ersatzavian/yellow_fuzz/sims/barbershop/1k_fft.PNG

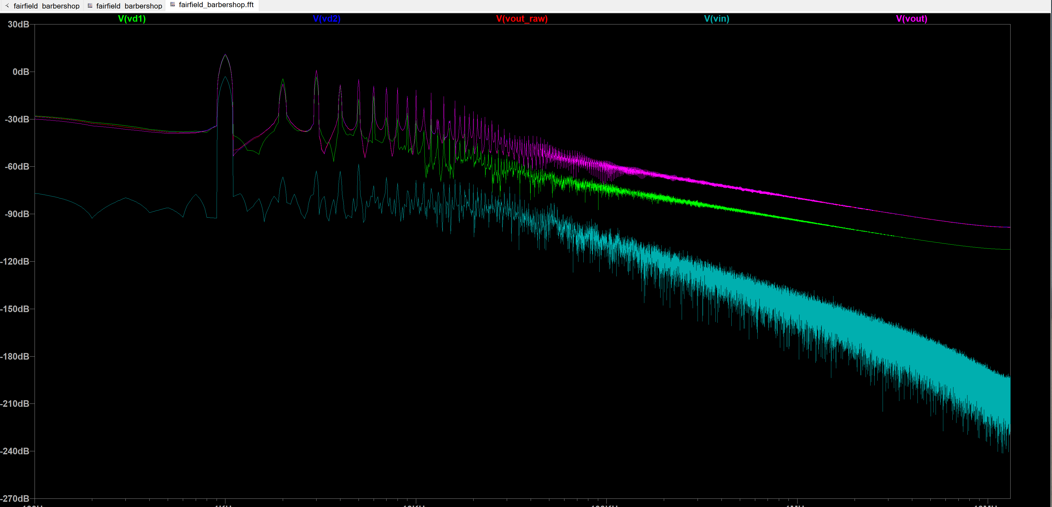
sims/barbershop/1k_fft.PNG
