ersatzavian/yellow_fuzz/sims/barbershop/1k_transient.PNG

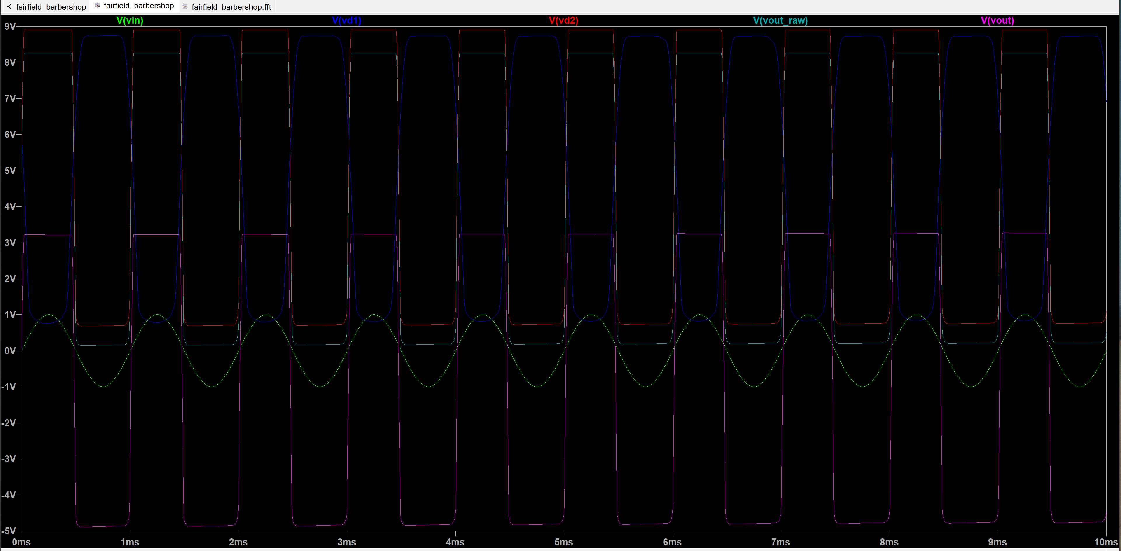
sims/barbershop/1k_transient.PNG
