ersatzavian/yellow_fuzz/sims/barbershop/base.PNG

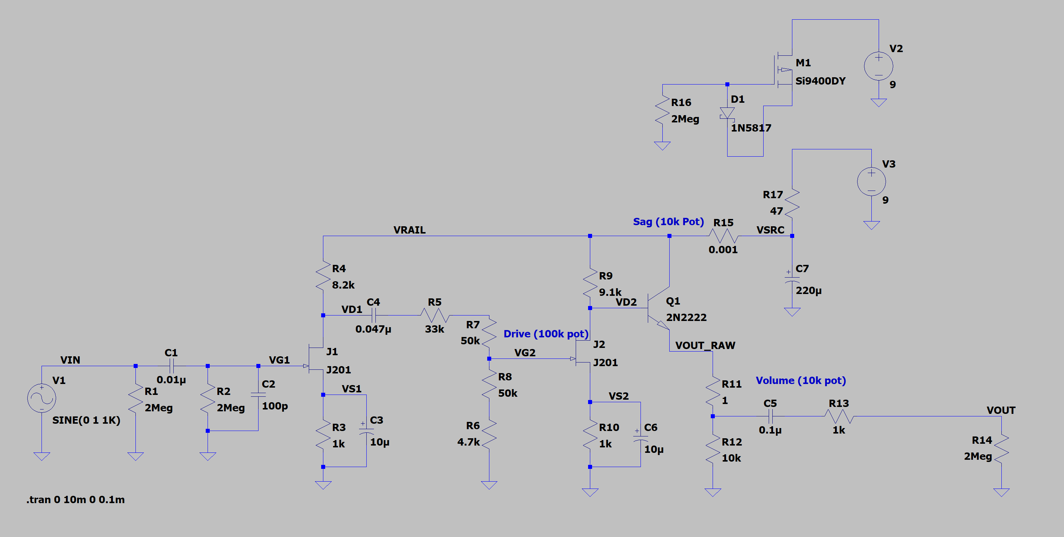
sims/barbershop/base.PNG
