ersatzavian/yellow_fuzz/sims/dist_input_hpf.png

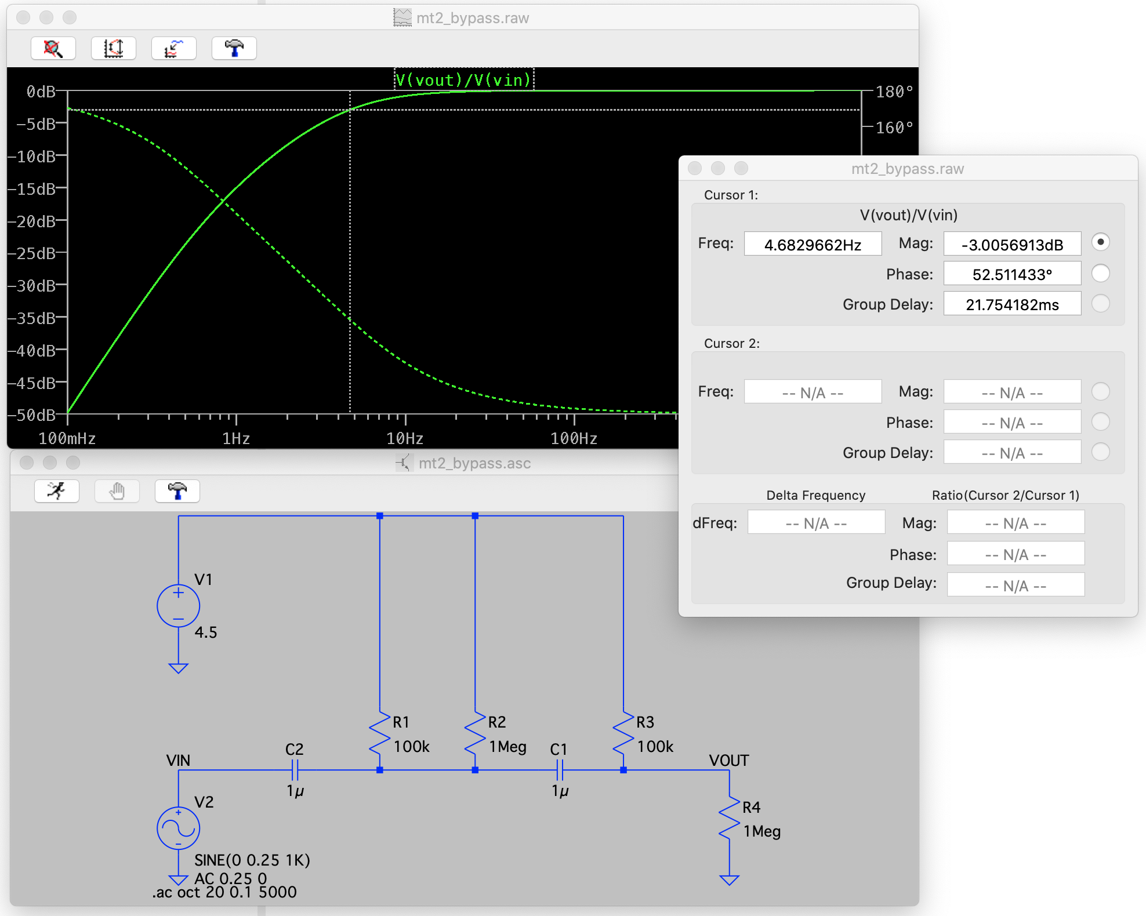
sims/dist_input_hpf.png
