ersatzavian/yellow_fuzz/sims/images/distortion_time.png

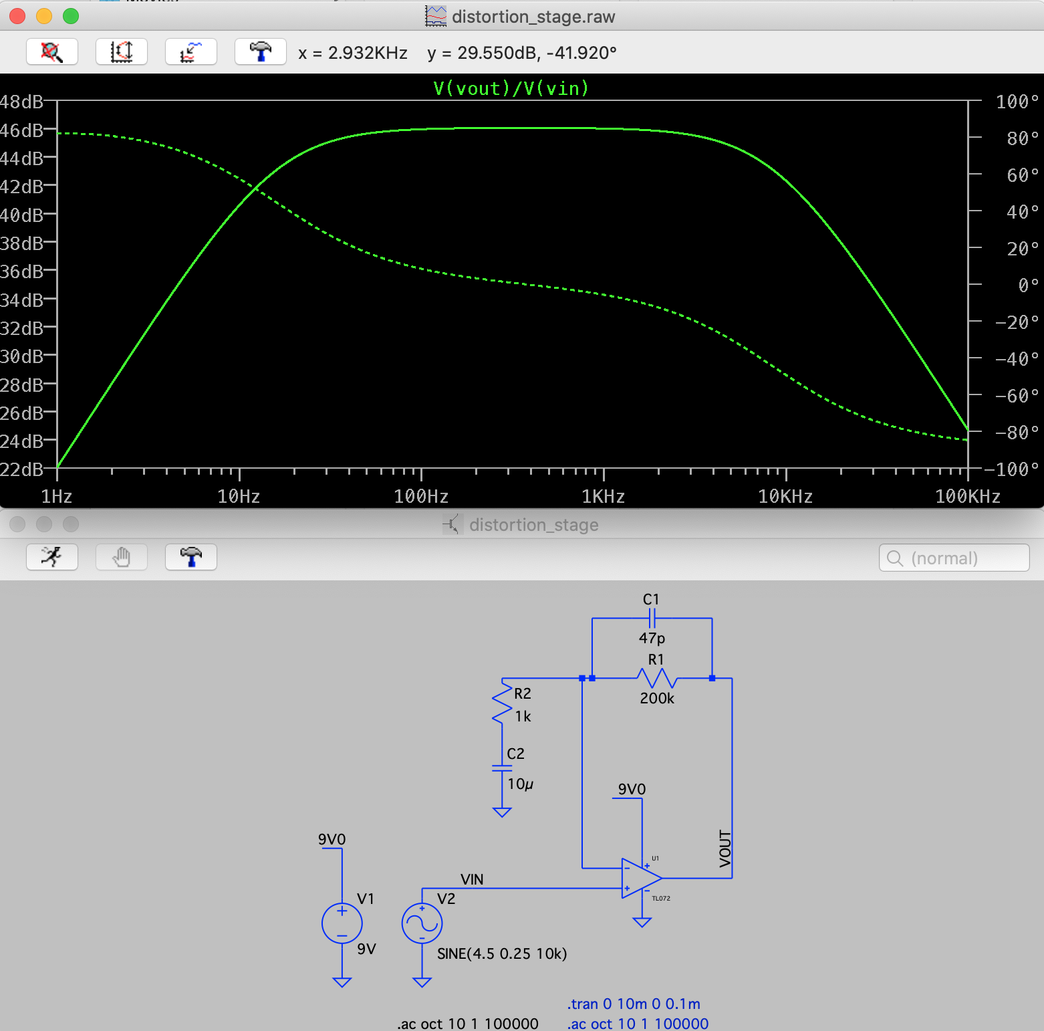
sims/images/distortion_time.png
