ersatzavian/yellow_fuzz/sims/images/predistortion_bpf_mod.png

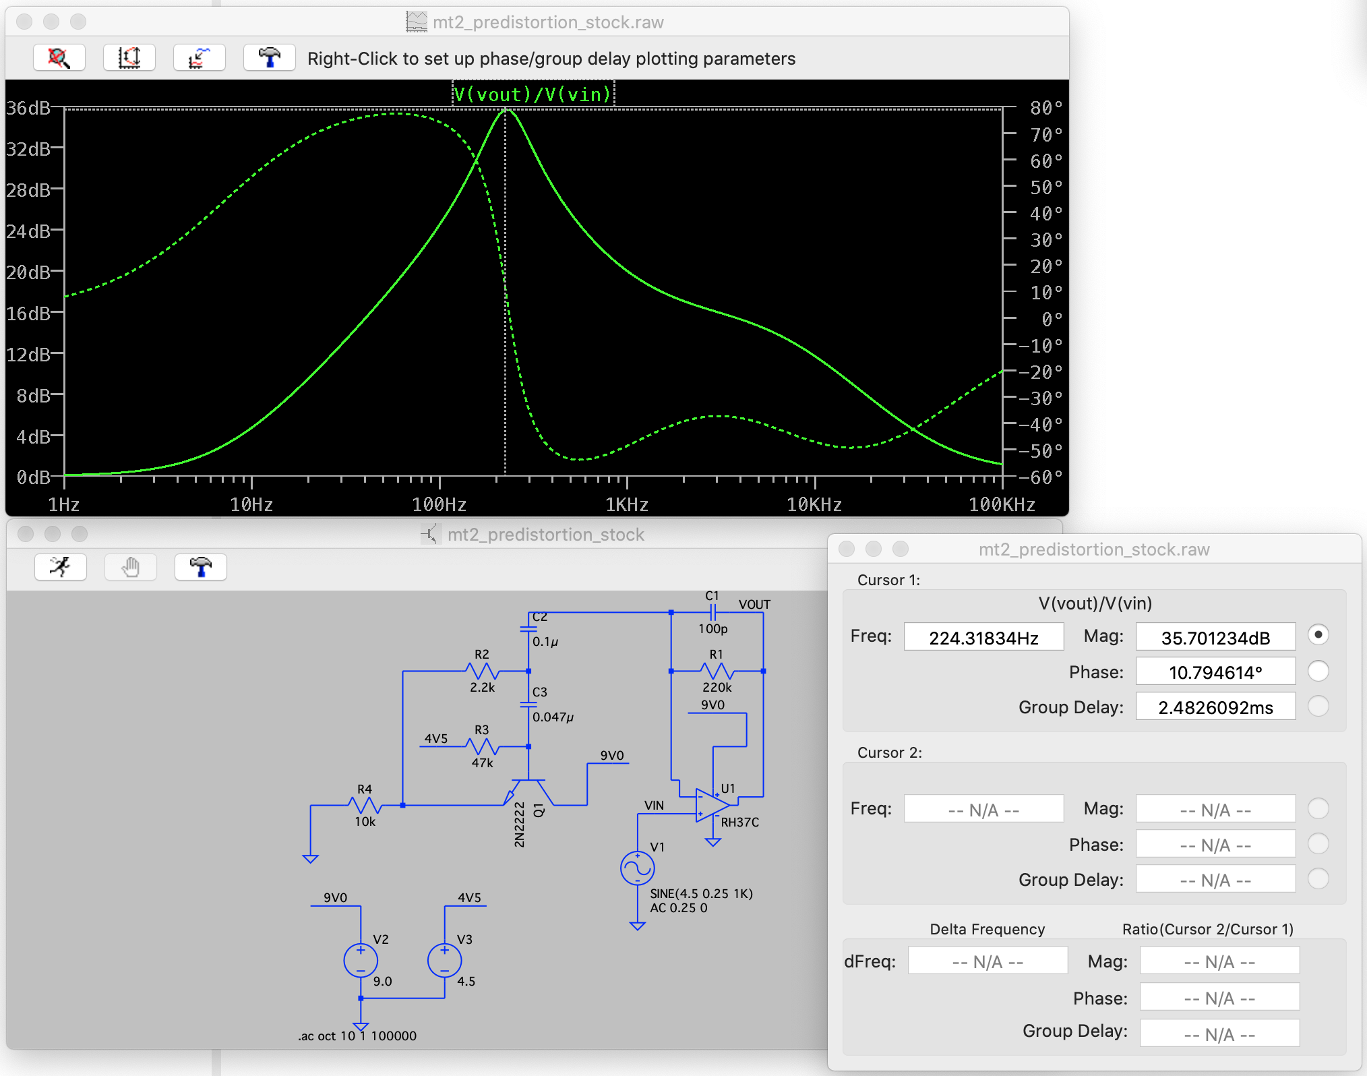
sims/images/predistortion_bpf_mod.png
