ersatzavian/yellow_fuzz/sims/predistortion_output_bpf.png

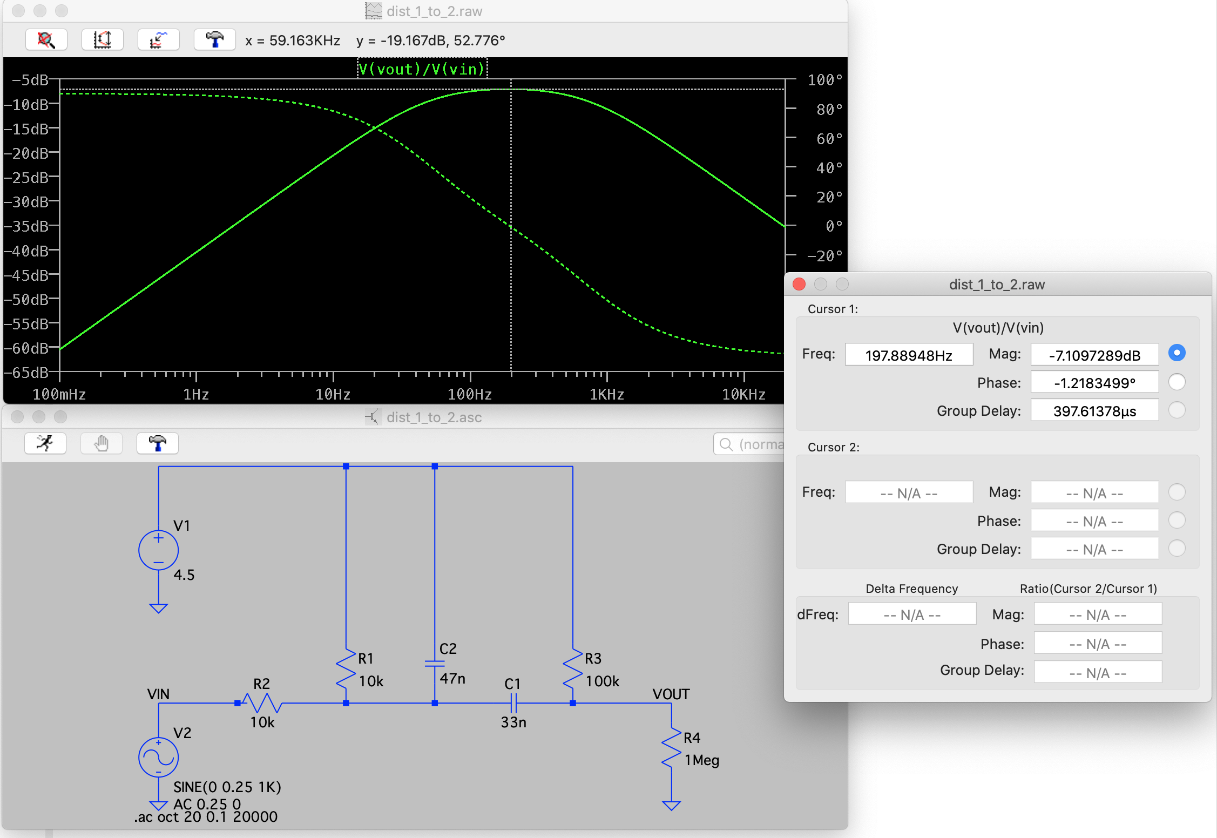
sims/predistortion_output_bpf.png
