ersatzavian/yellow_fuzz/parts/PTV111-4420A.stp

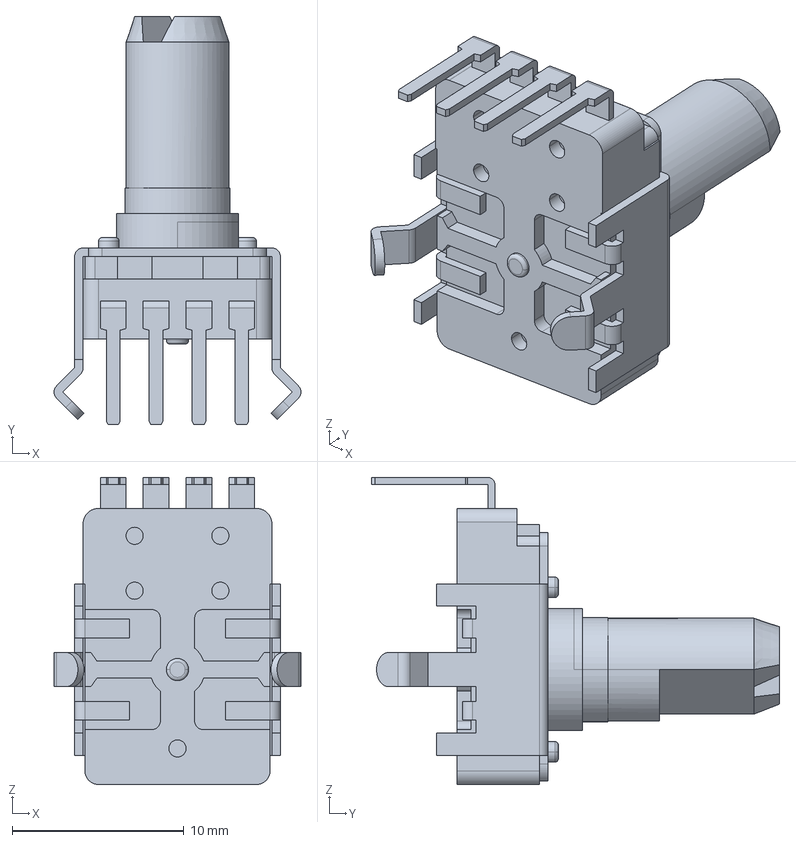
[picture p37: CAD file, 2020-02-02]
parts/PTV111-4420A.stp
14.4 x 23.8 x 17.9 mm
