ersatzavian/yellow_fuzz/parts/3362P001XXX0A.stp

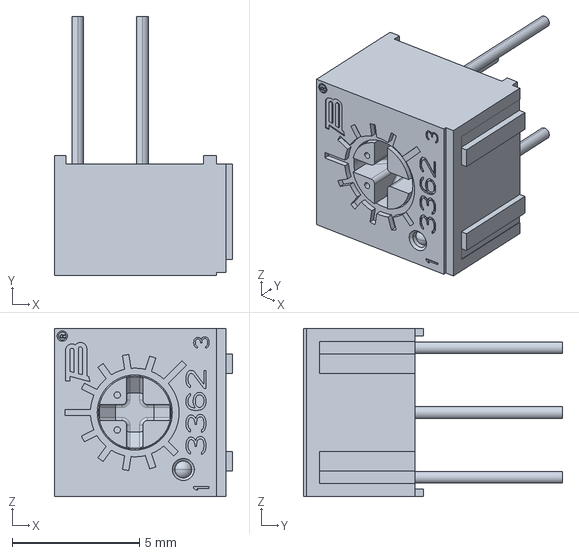
[picture p38: CAD file, 2020-04-22]
parts/3362P001XXX0A.stp
6.98 x 10.2 x 6.60 mm
