ersatzavian/yellow_fuzz/sims/distortion_stage.asc

C1: cap; 47p
C2: cap; 10µ
C3: cap; 10µ
C4: cap; 15n
D1: diode; 1N4148
D2: diode; 1N4148
R1: res; 200k
R2: res; 1k
R3: res; 2.2k
R4: res; 10k
R5: res; 4.7k
R6: res; 100k
U1: TL072
V1: voltage; 9V
V2: signal; SINE(4.5 0.25 400); AC 1 0
V3: voltage; 4.5V
Named nets: 0, 9V0, VIN, VGAIN, 4V5, VOUT, VCLIP
.tran 0 10m 0 0.1m
.tran 0 10m 0 0.1m
.ac oct 10 1 100000
