ersatzavian/yellow_fuzz/sims/mt2_predistortion.asc

C1: cap; 100p
C2: cap; 0.027µ
C3: cap; 0.01µ
Q1: npn; 2N2222
R1: res; 220k
R2: res; 2.2k
R3: res; 47k
R4: res; 10k
U1: RH37C
V1: signal; SINE(4.5 0.25 1K); AC 0.25 0
V2: voltage; 9.0
V3: voltage; 4.5
Named nets: 0, 4V5, 9V0, VIN, VOUT
.ac oct 10 1 100000
