ersatzavian/yellow_fuzz/sims/dist_1_to_2.asc

C1: cap; 33n
C2: cap; 47n
R1: res; 10k
R2: res; 10k
R3: res; 100k
R4: res; 1Meg
V1: voltage; 4.5
V2: signal; SINE(0 0.25 1K); AC 0.25 0
Named nets: 0, VIN, VOUT
.ac oct 20 0.1 20000
