ersatzavian/yellow_fuzz/sims/mt2_input.asc

C1: cap; 47n
J1: njf; J201
R1: res; 10k
R2: res; 1Meg
R3: res; 10k
R4: res; 0.01
V1: signal; SINE(0 0.25 1K); AC 0.25 0
V2: voltage; 9
V3: voltage; 4.5
Named nets: 0, 9V0, 4V5, VOUT, VG, VIN
.ac dec 20 0.005 20000
