ersatzavian/yellow_fuzz/sims/j201.asc

J1: njf; J201
R1: res; 100
V1: voltage; 9
V2: voltage; 1
Named nets: 0
.dc V2 -8 0 0.1
