ersatzavian/yellow_fuzz/sims/mt2_bypass.asc

C1: cap; 0.1µ
C2: cap; 1µ; V=200 Irms=0 Rser=0 Lser=0
R1: res; 100k
R2: res; 1Meg
R3: res; 100k
R4: res; 1Meg
V1: voltage; 4.5
V2: signal; SINE(0 0.25 1K); AC 0.25 0
Named nets: 0, VIN, VOUT
.ac oct 20 0.1 5000
