ersatzavian/yellow_fuzz/sims/RC_IN.asc

C1: cap; 47n
R1: res; 10k
R2: res; 1Meg
V1: signal; AC 0.25 0
Named nets: 0, VIN, VOUT
