ersatzavian/yellow_fuzz/sims/barbershop/fairfield_barbershop.asc

C1: cap; 0.01µ; V=50 Irms=0 Rser=0 Lser=0 mfg="Murata" pn="GCM155R71H103KA55" type="X7R"
C2: cap; 100p; V=50 Irms=20.8m Rser=5.448 Lser=0 mfg="KEMET" pn="C0603C101K5RAC" type="X7R"
C3: polcap; 10µ; V=25 Irms=39m Rser=2.8 Lser=0 mfg="Nichicon" pn="UPR1E100MAH" type="Al electrolytic"
C4: cap; 0.047µ; V=25 Irms=0 Rser=0 Lser=0 mfg="Murata" pn="GCM155R71E473KA55" type="X7R"
C5: cap; 0.1µ; V=25 Irms=0 Rser=0 Lser=0 mfg="Murata" pn="GCM155R71E104KE02" type="X7R"
C6: polcap; 10µ; V=25 Irms=39m Rser=2.8 Lser=0 mfg="Nichicon" pn="UPR1E100MAH" type="Al electrolytic"
C7: polcap; 220µ; V=25 Irms=250m Rser=0.35 Lser=0 mfg="Nichicon" pn="UPR1E221MPH" type="Al electrolytic"
D1: schottky; 1N5817
J1: njf; J201
J2: njf; J201
M1: pmos; Si9400DY
Q1: npn; 2N2222
R1: res; 2Meg
R2: res; 2Meg
R3: res; 1k
R4: res; 8.2k
R5: res; 33k
R6: res; 4.7k
R7: res; 50k
R8: res; 50k
R9: res; 9.1k
R10: res; 1k
R11: res; 1
R12: res; 10k
R13: res; 1k
R14: res; 2Meg
R15: res; 0.001
R16: res; 2Meg
R17: res; 47
V1: signal; SINE(0 0 1K); AC 0.5
V2: voltage; 9
V3: voltage; 9
Named nets: 0, VOUT, VIN, VRAIL, VSRC, VG2, VD2, VOUT_RAW, VG1, VD1, VS1, VS2
Drive (100k pot)
Sag (10k Pot)
Volume (10k pot)
.ac oct 10 5 100k
